Weeeesen/calibrationKit/calibrationKit_v2/test_twist_friction_lock/bottomPiece.stl

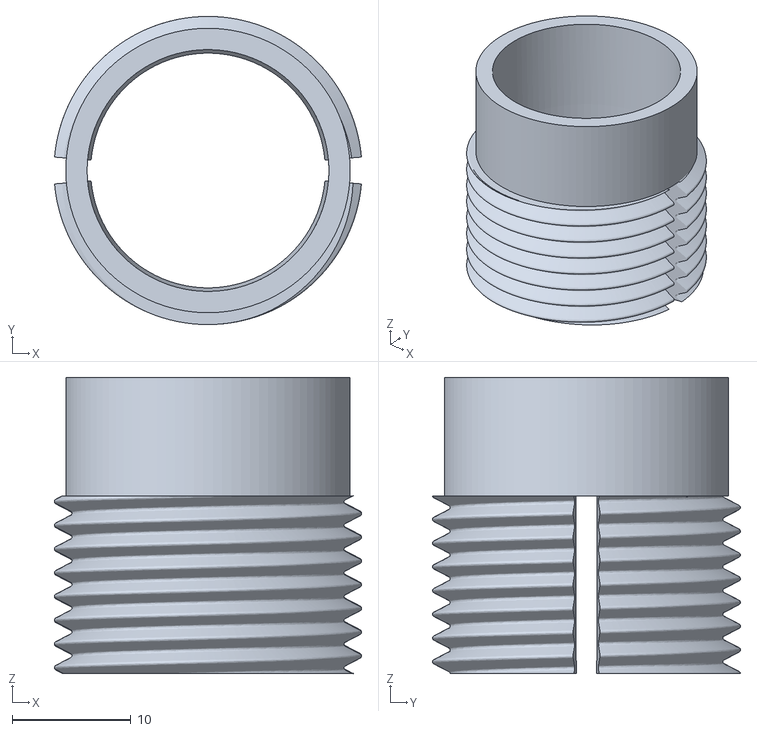
[picture p20: CAD file, 2022-07-05]
calibrationKit_v2/test_twist_friction_lock/bottomPiece.stl
25.9 x 26.0 x 25.0
