Weeeesen/calibrationKit/calibrationKit_v2/wand/prototype_for_circuit&connections/prototype_5_batteryPart.stl

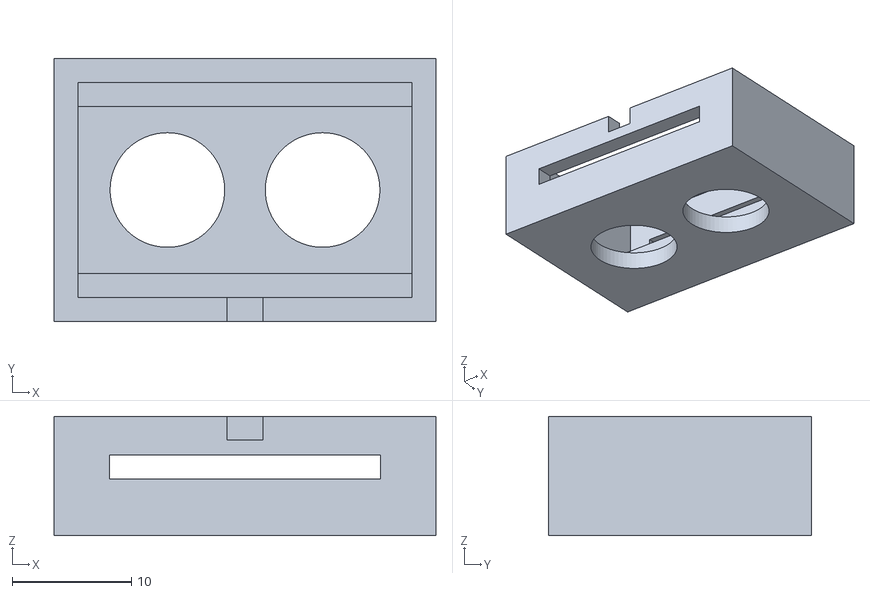
[picture p21: CAD file, 2022-06-22]
calibrationKit_v2/wand/prototype_for_circuit&connections/prototype_5_batteryPart.stl
32.0 x 22.0 x 10.0
