Weeeesen/calibrationKit/calibrationKit_v2/wand/prototype_for_circuit&connections/prototype_5_sliderPart.stl

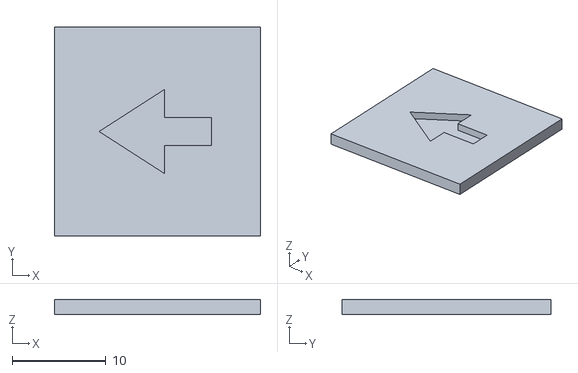
[picture p22: CAD file, 2022-06-22]
calibrationKit_v2/wand/prototype_for_circuit&connections/prototype_5_sliderPart.stl
22.0 x 22.3 x 1.60
